phazil/Purple-Project-Redux/Images/OpenStickCommunity Posts/1/IMG_7995.jpg

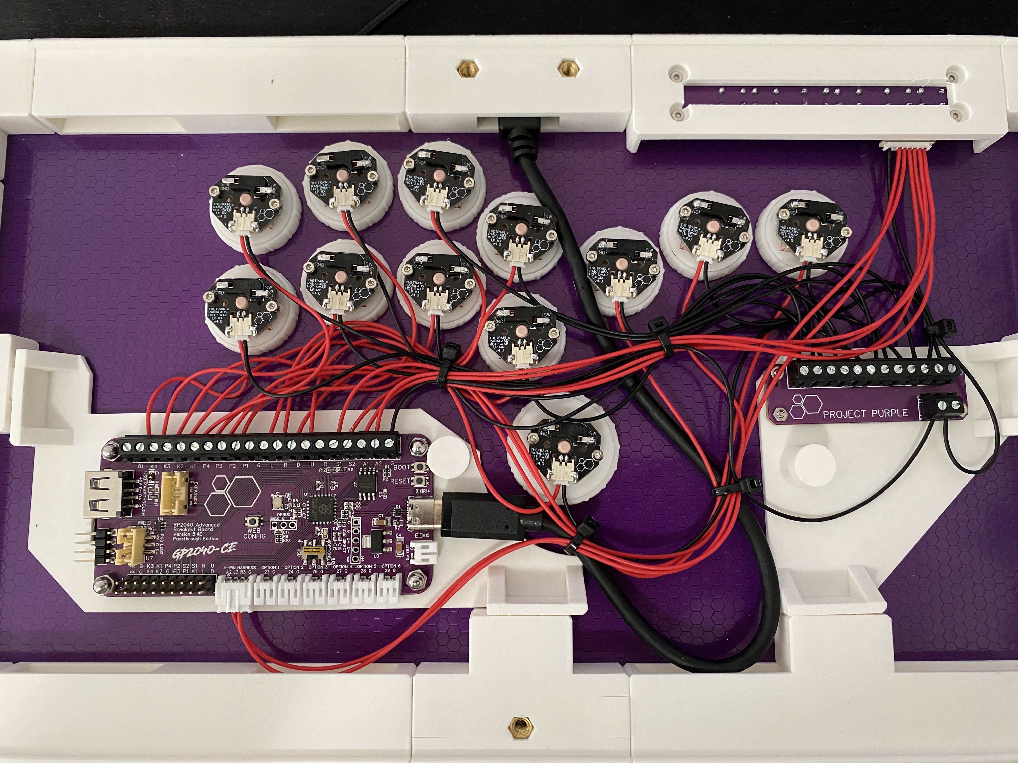
Images/OpenStickCommunity Posts/1/IMG_7995.jpg
