phazil/Purple-Project-Redux/Images/OpenStickCommunity Posts/1/IMG_7997.jpg

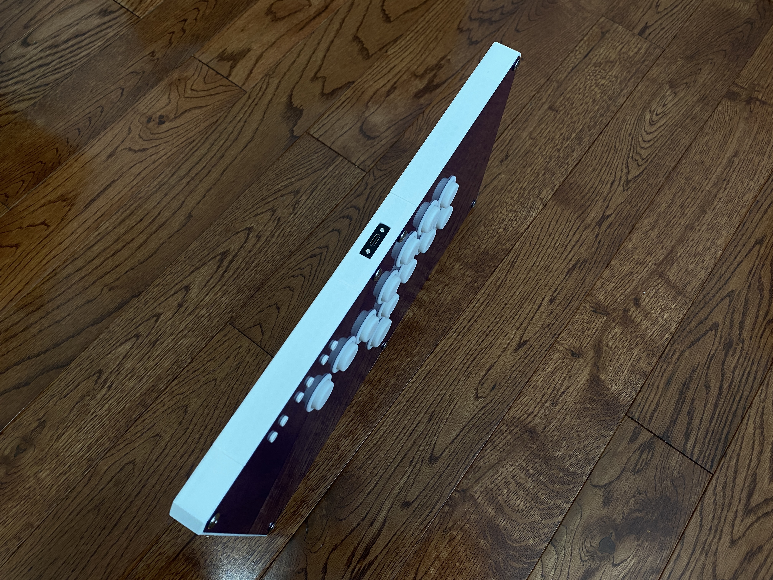
Images/OpenStickCommunity Posts/1/IMG_7997.jpg
