phazil/Purple-Project-Redux/Images/OpenStickCommunity Posts/1/IMG_7999.jpg

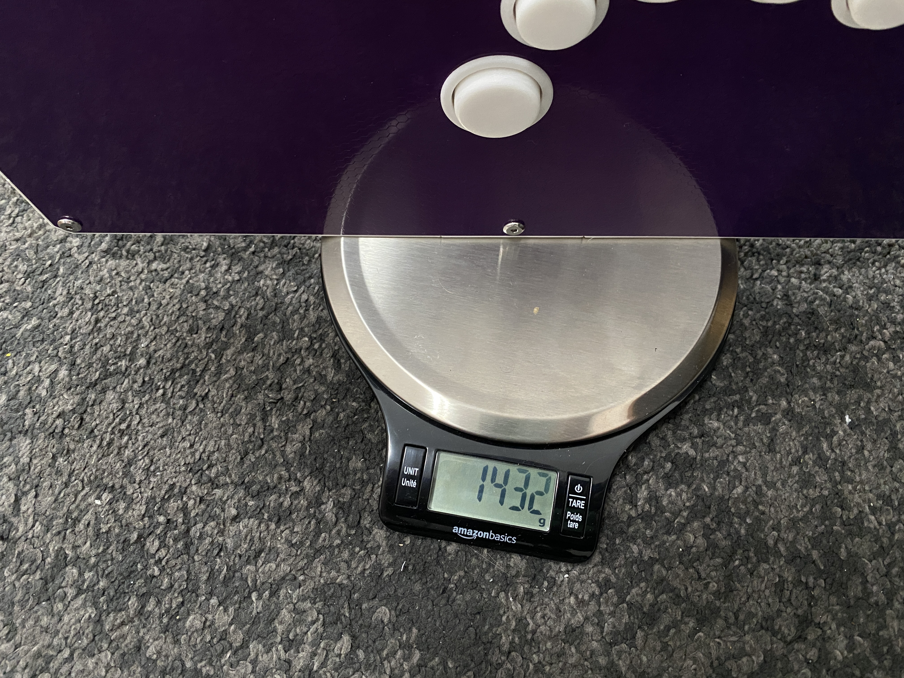
Images/OpenStickCommunity Posts/1/IMG_7999.jpg
