phazil/Purple-Project-Redux/Images/OpenStickCommunity Posts/2/IMG_8071.jpg

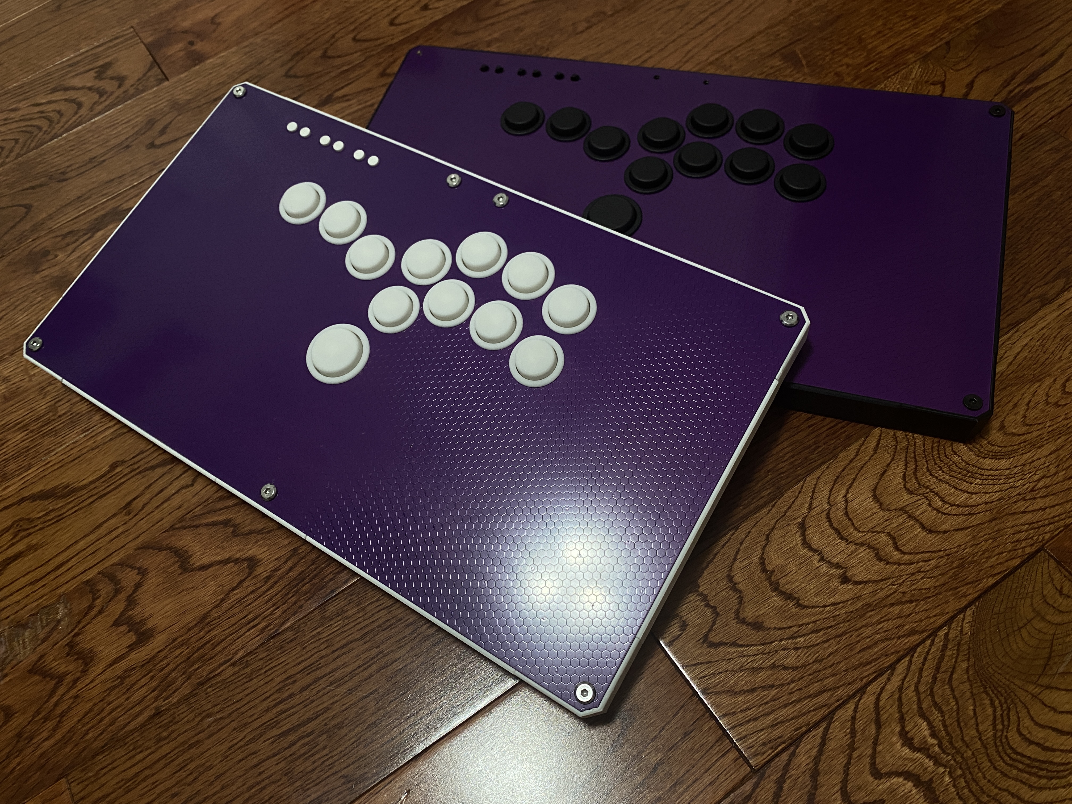
Images/OpenStickCommunity Posts/2/IMG_8071.jpg
