phazil/Purple-Project-Redux/Images/OpenStickCommunity Posts/2/IMG_8072.jpg

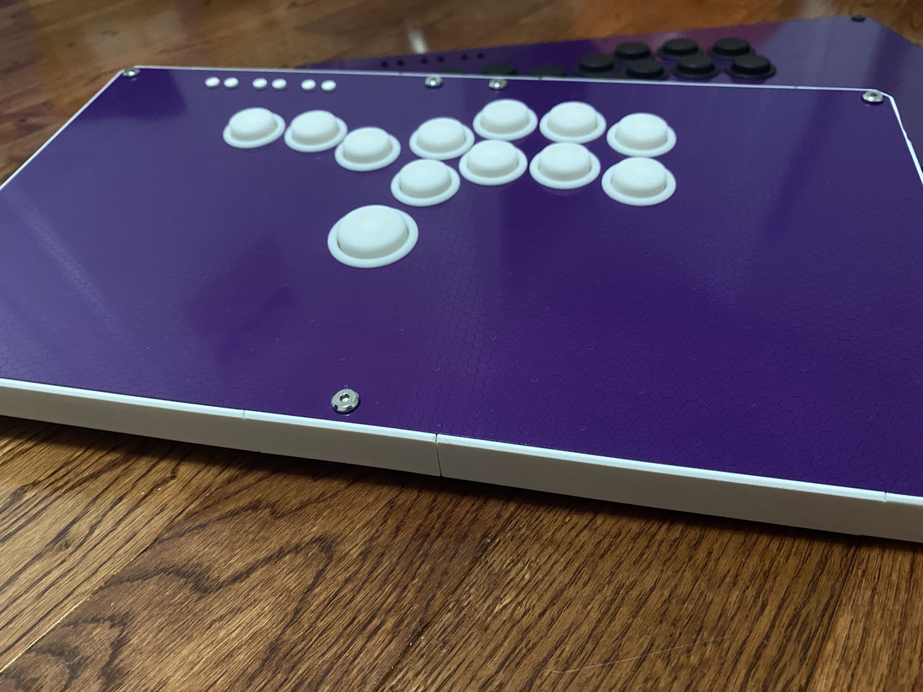
Images/OpenStickCommunity Posts/2/IMG_8072.jpg
