phazil/Purple-Project-Redux/For Makers/STLs/Original + Acrylic/SticklessPLUS STLs/Top Middle StickPLUS  Acrylic.stl

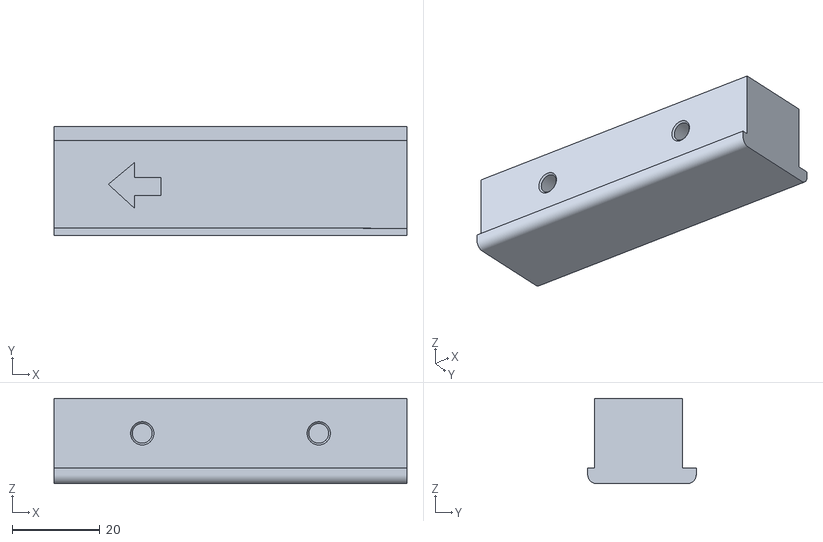
[picture p23: CAD file, 2024-10-15]
For Makers/STLs/Original + Acrylic/SticklessPLUS STLs/Top Middle StickPLUS Acrylic.stl
80.3 x 24.7 x 19.4
