phazil/Purple-Project-Redux/Source Files/KiCAD Files/MenuPanel/MenuPanel.step

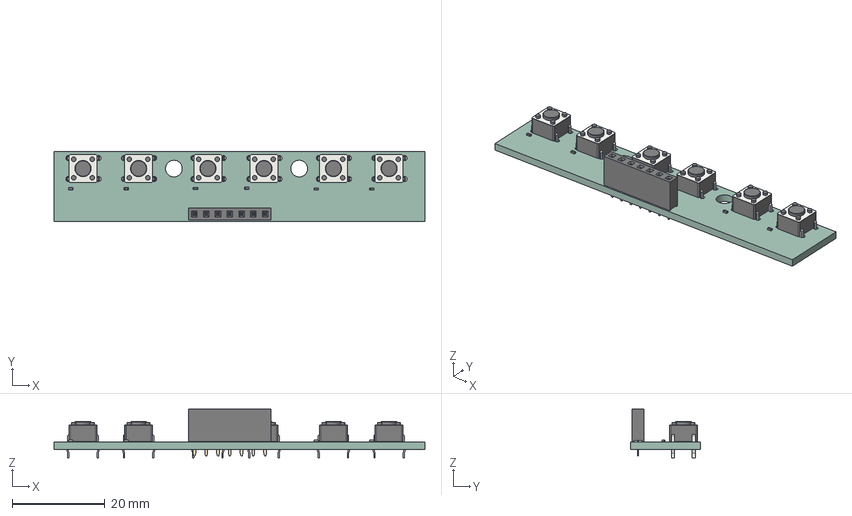
[picture p24: CAD file, 2024-09-29]
Source Files/KiCAD Files/MenuPanel/MenuPanel.step
80.0 x 15.0 x 10.5 mm
SW_PUSH_6mm_h4.3mm x 6
R_0402_1005Metric x 6
PinSocket_1x07_P254mm_Vertical
MenuPanel_PCB
