phazil/Purple-Project-Redux/Source Files/Panel DXFs/SticklessPLUS.dxf

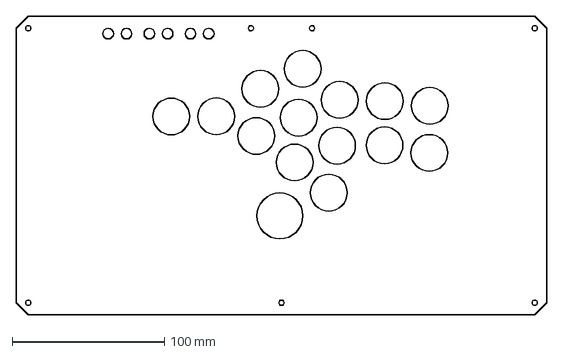
[picture p25: CAD file, 2024-10-15]
Source Files/Panel DXFs/SticklessPLUS.dxf
348.6 x 196.2 mm
