phazil/Purple-Project-Redux/Source Files/STEP Files/Original/Bottom Left.step

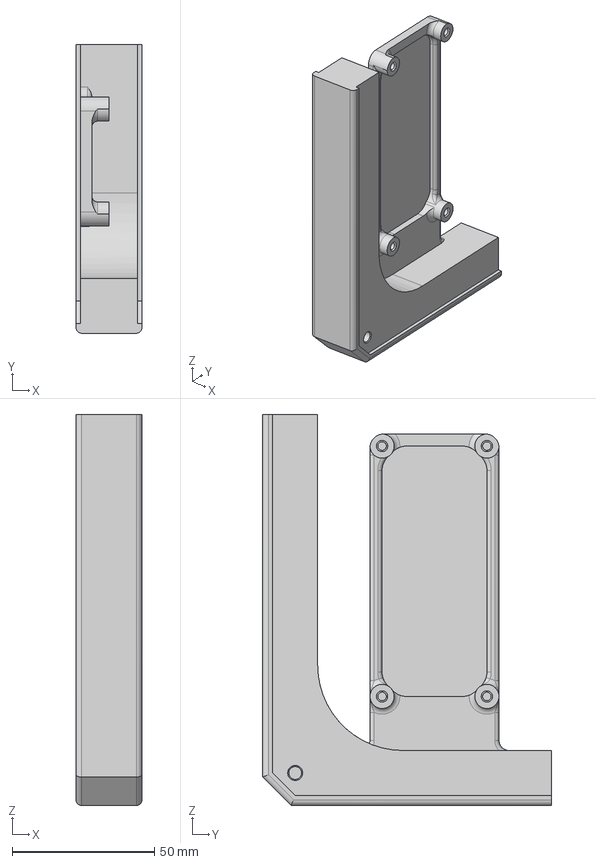
[picture p26: CAD file, 2024-10-15]
Source Files/STEP Files/Original/Bottom Left.step
23.2 x 101.6 x 137.6 mm
