phazil/Purple-Project-Redux/For Makers/STLs/Original + Acrylic/Bottom Left Acrylic.stl

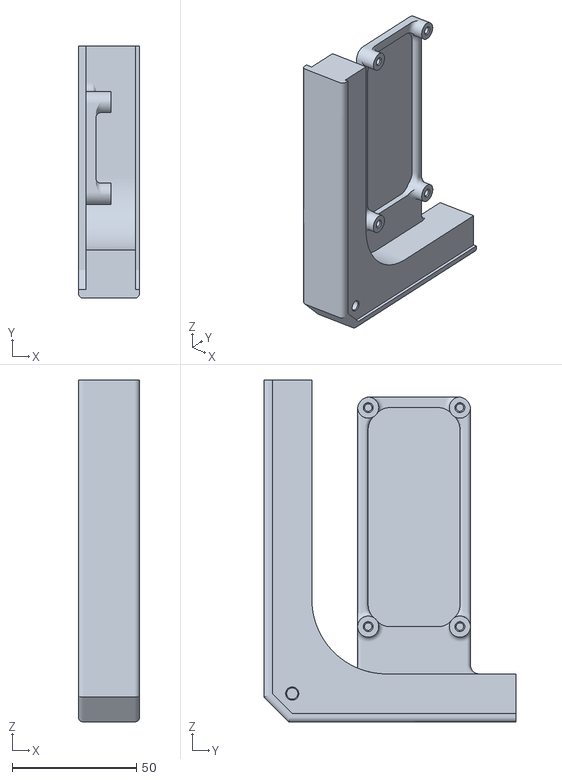
[picture p27: CAD file, 2024-10-15]
For Makers/STLs/Original + Acrylic/Bottom Left Acrylic.stl
24.7 x 101.6 x 137.6
