phazil/Purple-Project-Redux/For Makers/STLs/Original/Bottom Middle.stl

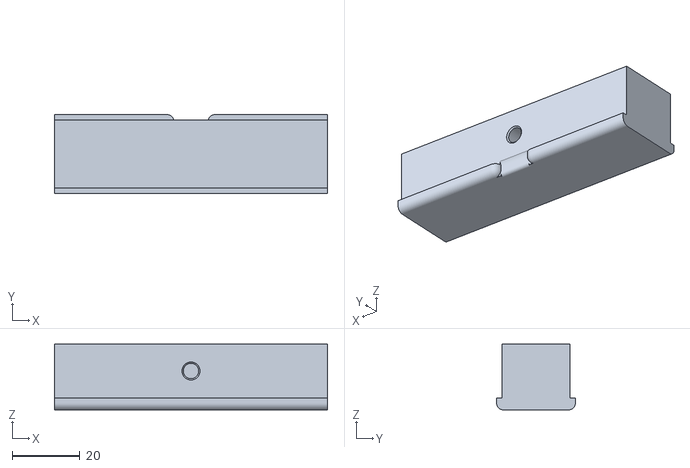
[picture p28: CAD file, 2024-10-15]
For Makers/STLs/Original/Bottom Middle.stl
80.3 x 23.2 x 19.4
