phazil/Purple-Project-Redux/For Makers/STLs/Original/SticklessPLUS STLs/Top Middle StickPLUS.stl

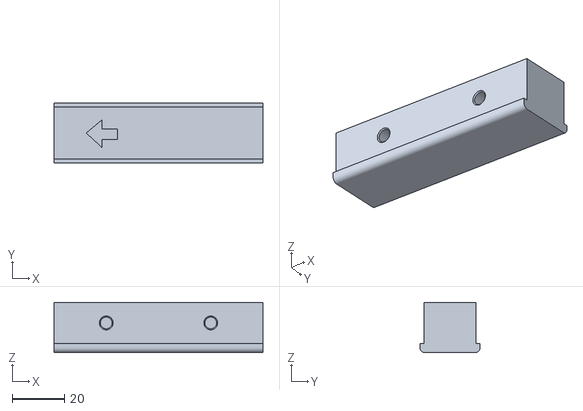
[picture p29: CAD file, 2024-10-15]
For Makers/STLs/Original/SticklessPLUS STLs/Top Middle StickPLUS.stl
80.3 x 23.2 x 19.4
