phazil/Purple-Project-Redux/Source Files/STEP Files/Original/Top Middle.step

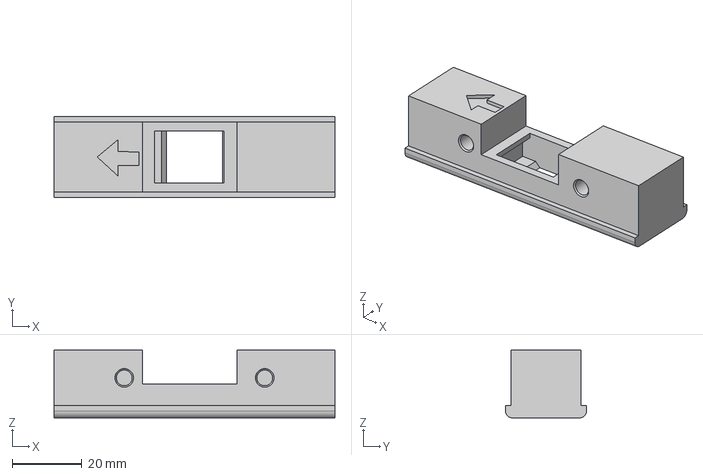
[picture p30: CAD file, 2024-10-15]
Source Files/STEP Files/Original/Top Middle.step
80.3 x 23.2 x 19.4 mm
