phazil/Purple-Project-Redux/Source Files/STEP Files/Orignal + Acrylic/SticklessPLUS STEP/Top Middle StickPLUS Acrylic.step

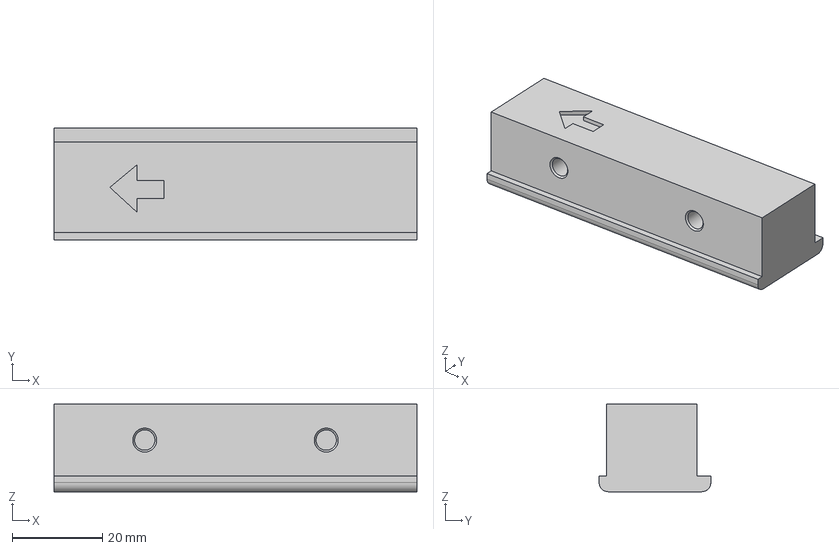
[picture p31: CAD file, 2024-10-15]
Source Files/STEP Files/Orignal + Acrylic/SticklessPLUS STEP/Top Middle StickPLUS Acrylic.step
80.3 x 24.7 x 19.4 mm
