phazil/Purple-Project-Redux/For Makers/Panel DXFs/Back Panel.dxf

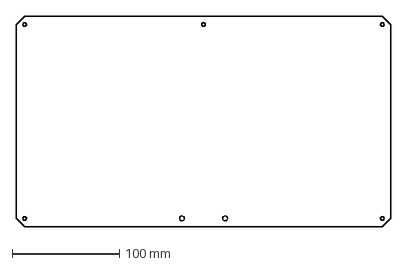
[picture p32: CAD file, 2024-09-29]
For Makers/Panel DXFs/Back Panel.dxf
348.6 x 196.2 mm
