phazil/Purple-Project-Redux/For Makers/STLs/Original + Acrylic/Top Middle Acrylic.stl

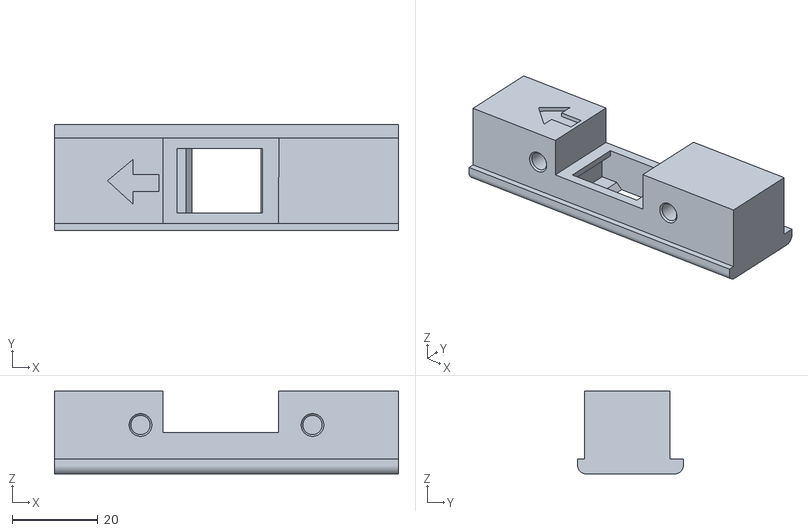
[picture p33: CAD file, 2024-10-15]
For Makers/STLs/Original + Acrylic/Top Middle Acrylic.stl
80.3 x 24.7 x 19.4
